jjtpawlik/urbicum-ventilaid/STEP files/BellowSlideGuard_PLA.STEP

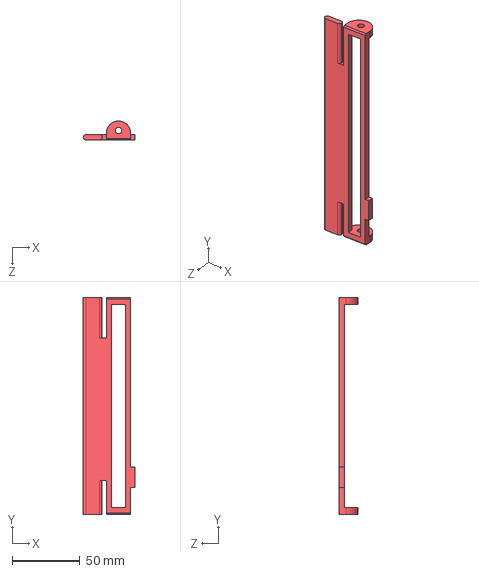
[picture p16: CAD file, 2020-03-23]
STEP files/BellowSlideGuard_PLA.STEP
38.0 x 160.0 x 14.0 mm
