jjtpawlik/urbicum-ventilaid/CAD Project/CAD Files - Solidworks/endstop_supplier.SLDPRT

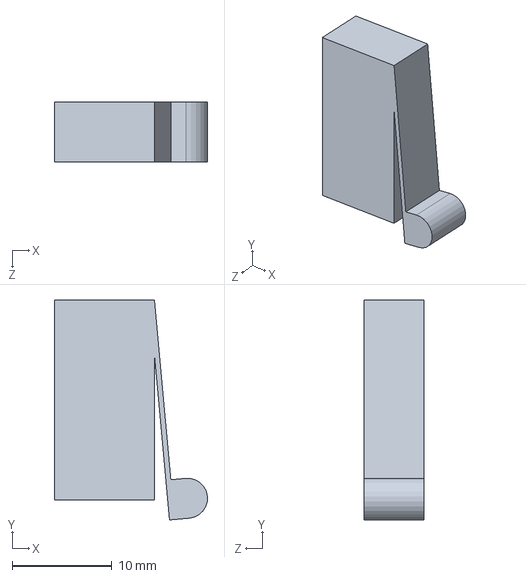
[picture p17: CAD file, 2020-03-23]
CAD Project/CAD Files - Solidworks/endstop_supplier.SLDPRT
15.3 x 22.0 x 6.00 mm
