jjtpawlik/urbicum-ventilaid/STEP files/BellowPiston_PLA.STEP

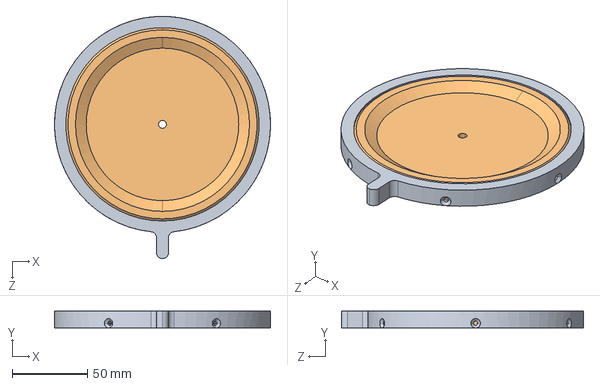
[picture p18: CAD file, 2020-03-23]
STEP files/BellowPiston_PLA.STEP
144.0 x 11.0 x 161.5 mm
