jjtpawlik/urbicum-ventilaid/CAD Project/CAD Files - Solidworks/CheckValveDisc_elastic.SLDPRT

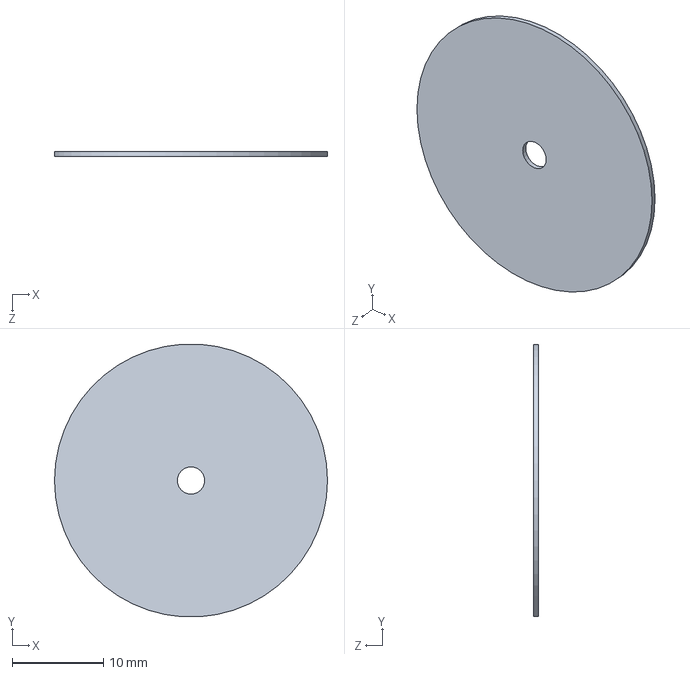
[picture p19: CAD file, 2020-03-23]
CAD Project/CAD Files - Solidworks/CheckValveDisc_elastic.SLDPRT
30.0 x 29.9 x 0.5 mm
