jjtpawlik/urbicum-ventilaid/STEP files/BellowBottomCap_PLA.STEP

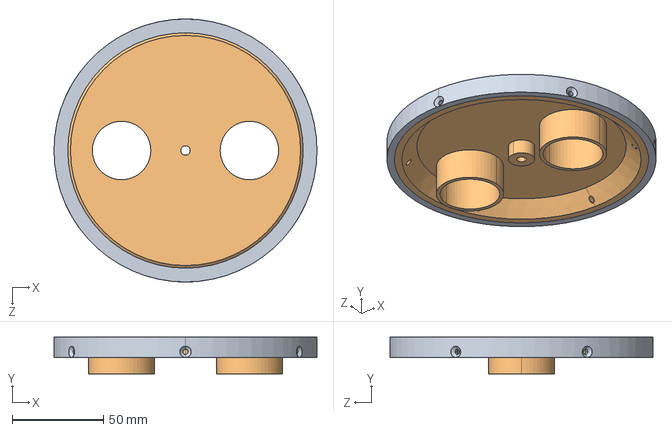
[picture p20: CAD file, 2020-03-23]
STEP files/BellowBottomCap_PLA.STEP
144.0 x 20.0 x 144.0 mm
