jjtpawlik/urbicum-ventilaid/STEP files/Bellow_soft_filament.STEP

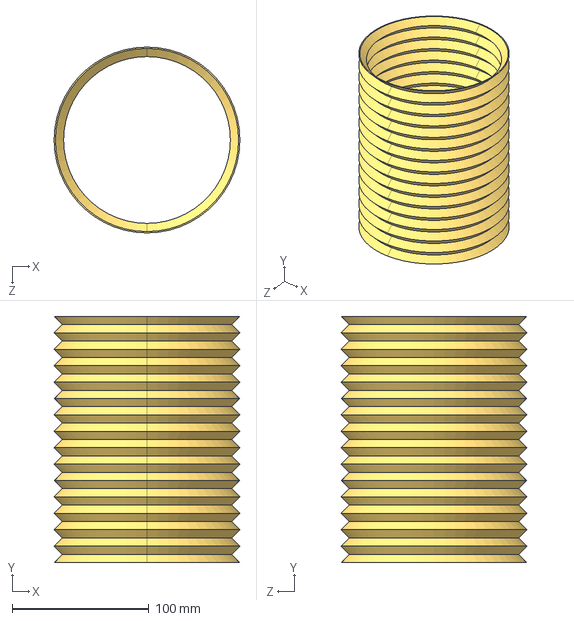
[picture p21: CAD file, 2020-03-23]
STEP files/Bellow_soft_filament.STEP
136.0 x 180.0 x 136.0 mm
