jjtpawlik/urbicum-ventilaid/CAD Project/CAD Files - Solidworks/3WayPneumaticControlValve_supplier.SLDPRT

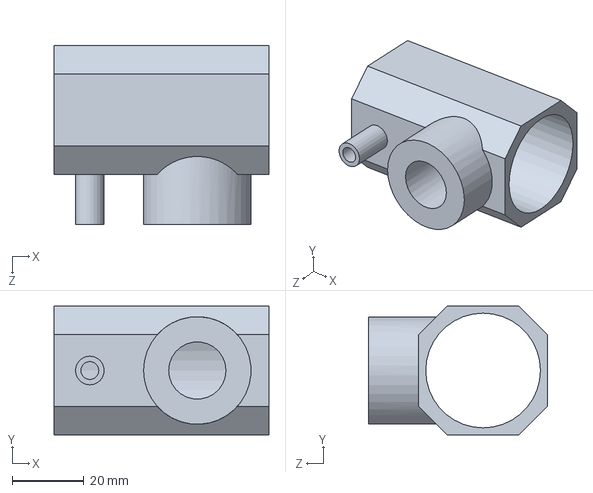
[picture p22: CAD file, 2020-03-23]
CAD Project/CAD Files - Solidworks/3WayPneumaticControlValve_supplier.SLDPRT
60.0 x 36.0 x 50.0 mm
